cheehieu/afternoon-cape/images/capes_display_back.jpg

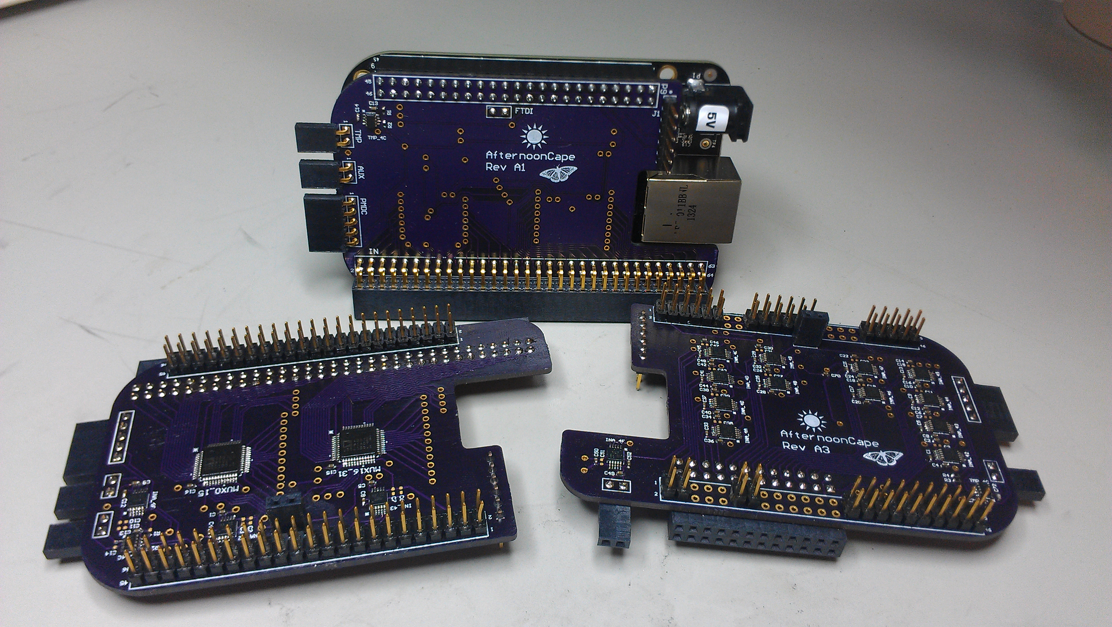
images/capes_display_back.jpg
