cheehieu/afternoon-cape/images/pmcape_A1_oshpark_bottom.png

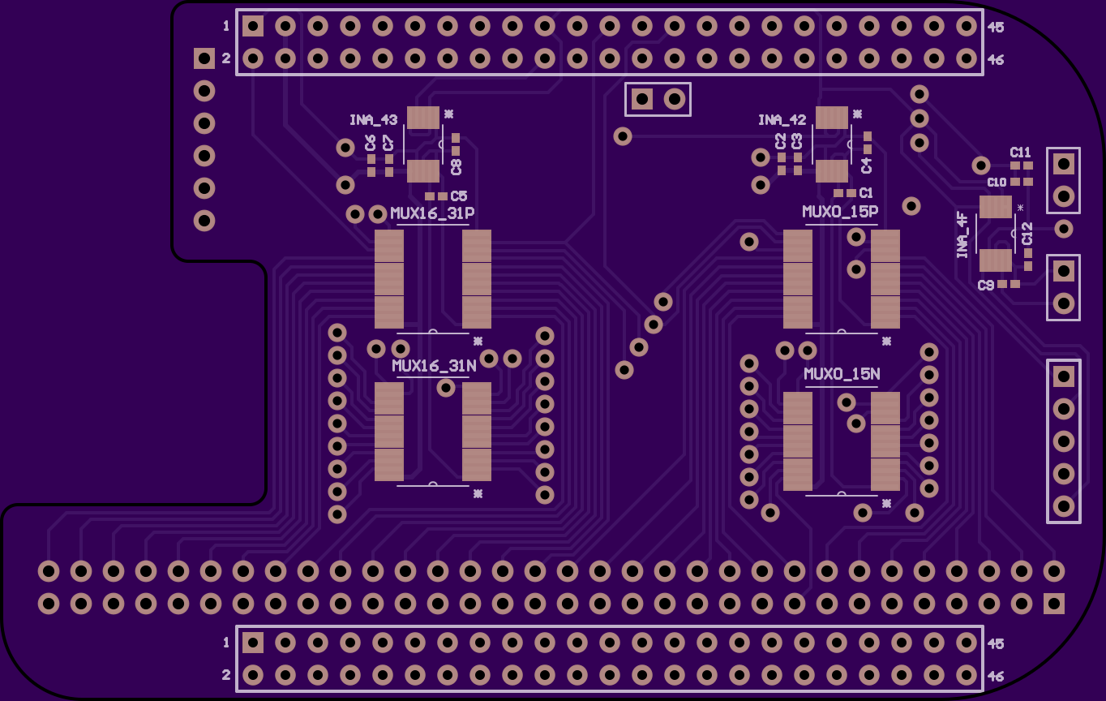
images/pmcape_A1_oshpark_bottom.png
