cheehieu/afternoon-cape/images/pmcape_A3_oshpark_bottom.png

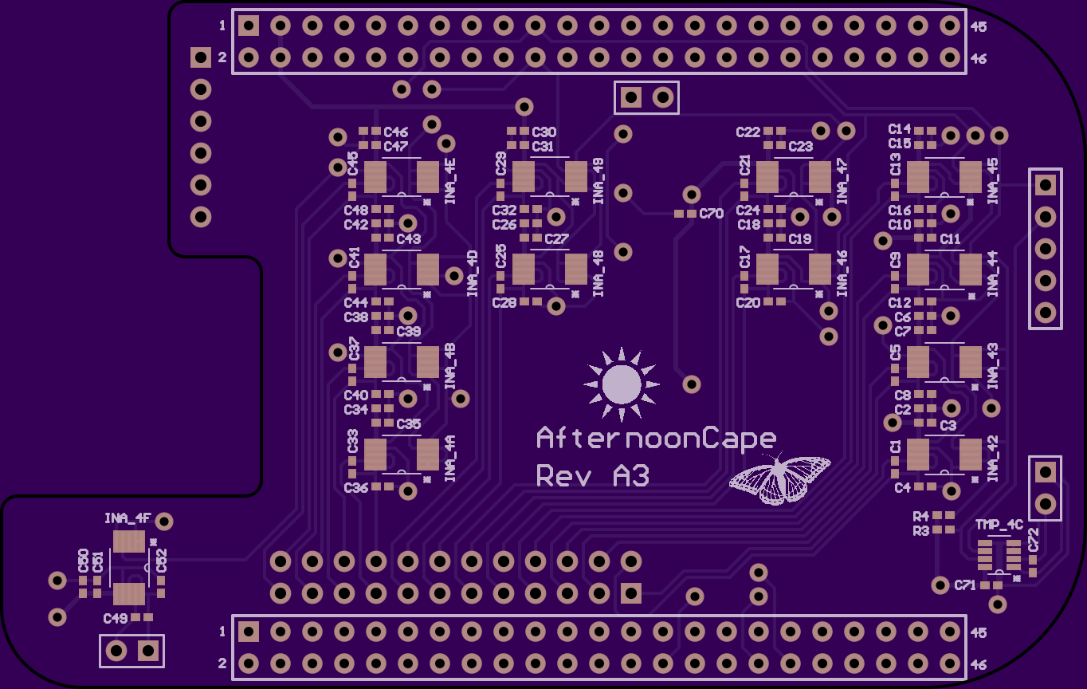
images/pmcape_A3_oshpark_bottom.png
