cheehieu/afternoon-cape/images/pmcape_board.jpg

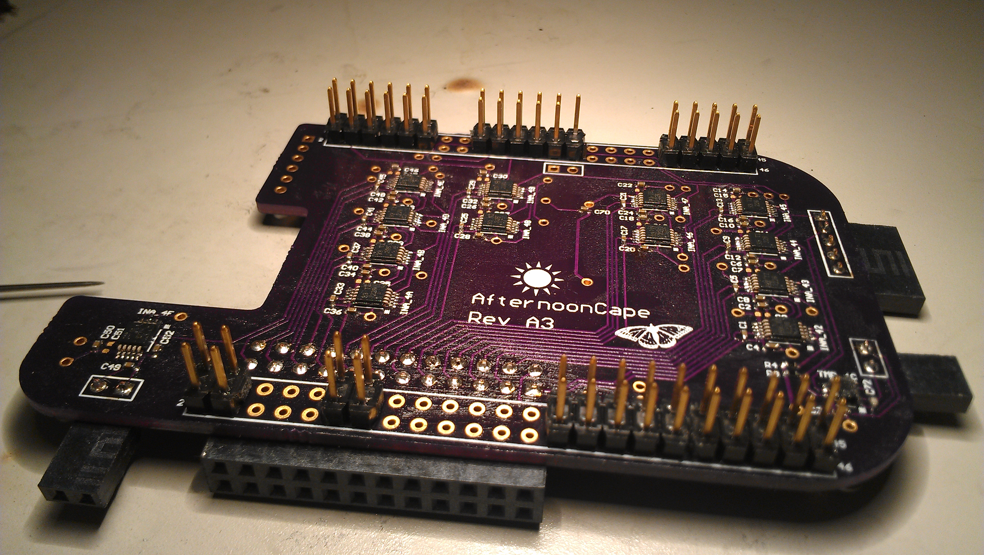
images/pmcape_board.jpg
