cheehieu/afternoon-cape/silk/black-sun-md.png

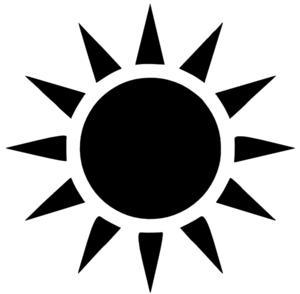
silk/black-sun-md.png
