cheehieu/afternoon-cape/silk/butterfly2.jpg

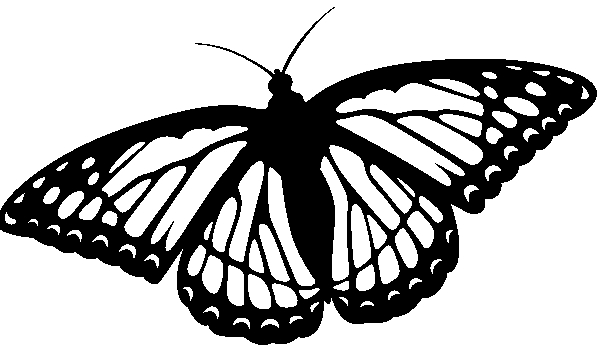
silk/butterfly2.jpg
