cheehieu/afternoon-cape/silk/butterfly.jpg

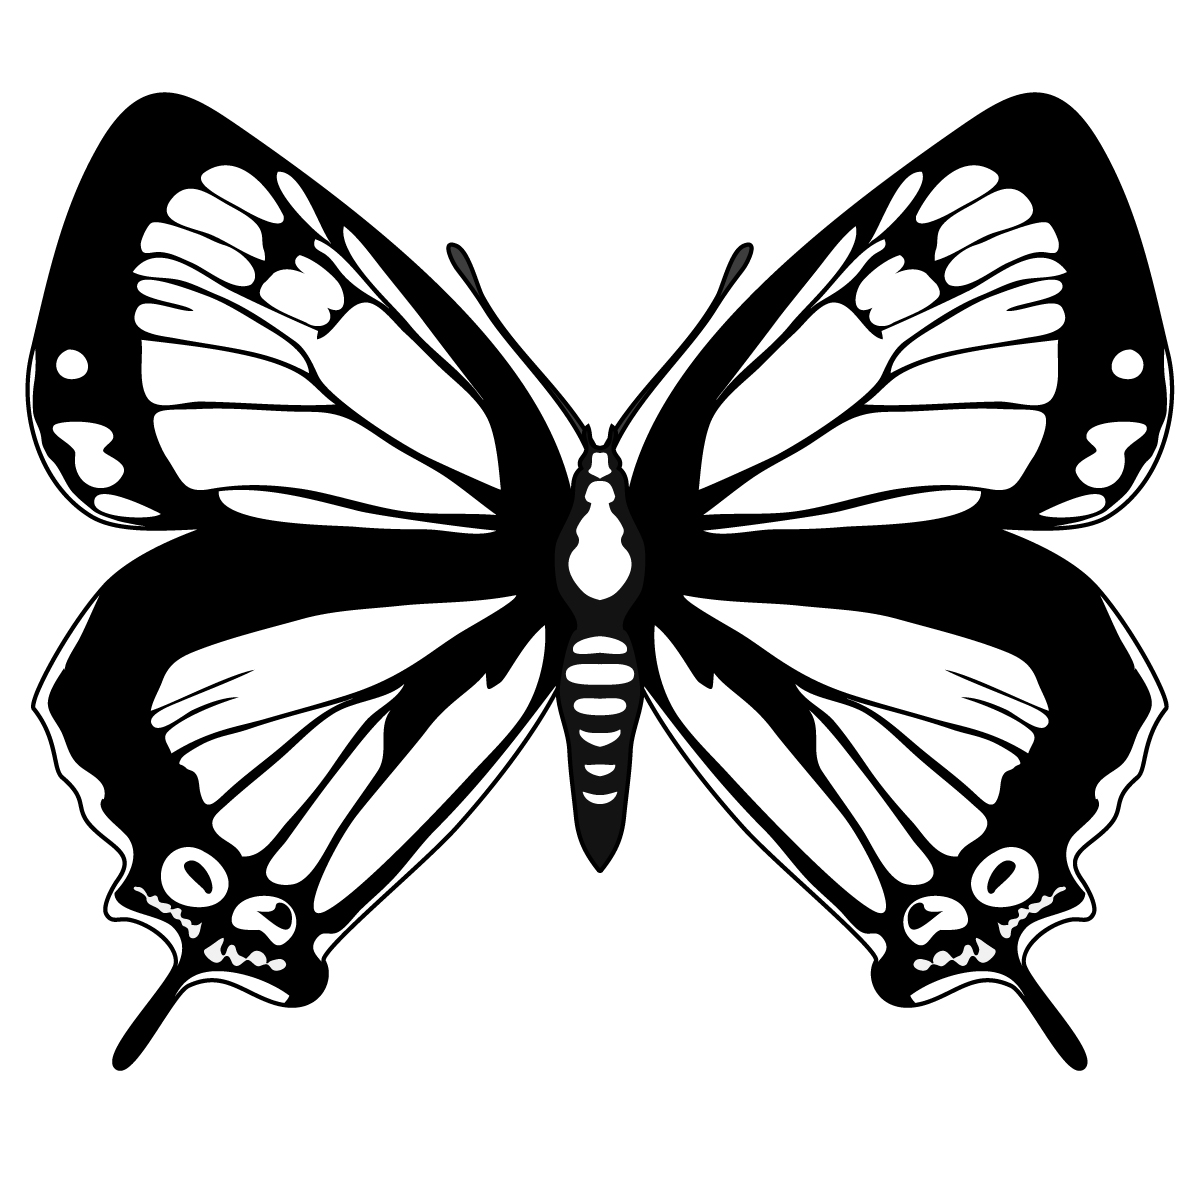
silk/butterfly.jpg
